gadjet/Window-Door-Sensor-V3/V3 Bottom.jpg

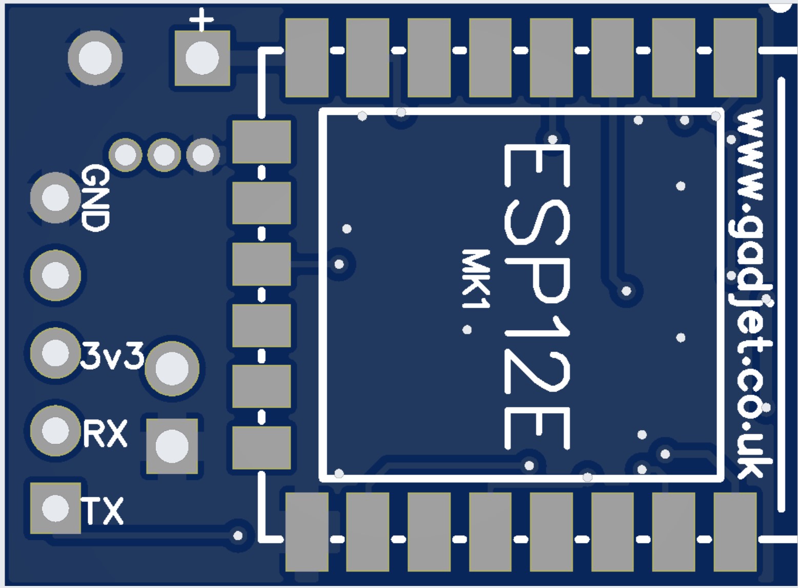
V3 Bottom.jpg
